t-mac81/pi-weather-station/images/IMG_1845.jpg

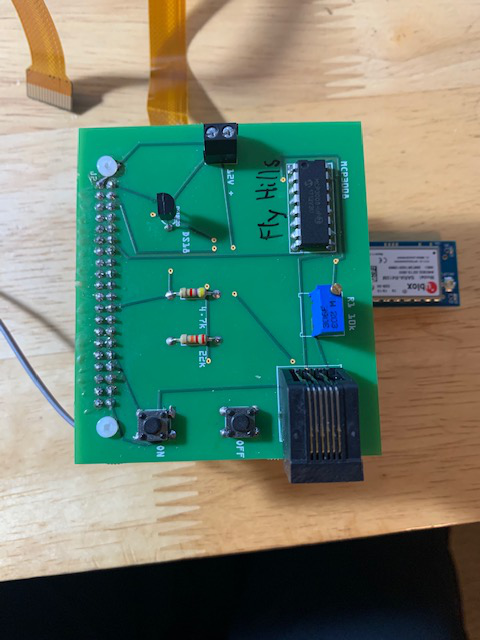
images/IMG_1845.jpg
