t-mac81/pi-weather-station/images/IMG_1846.jpg

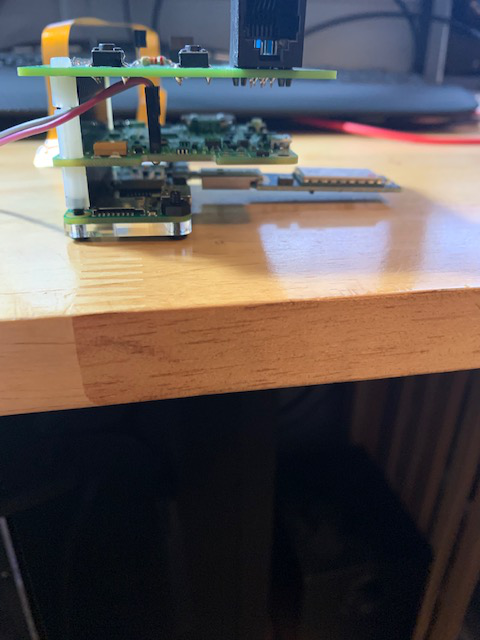
images/IMG_1846.jpg
