t-mac81/pi-weather-station/images/IMG_2492.JPG

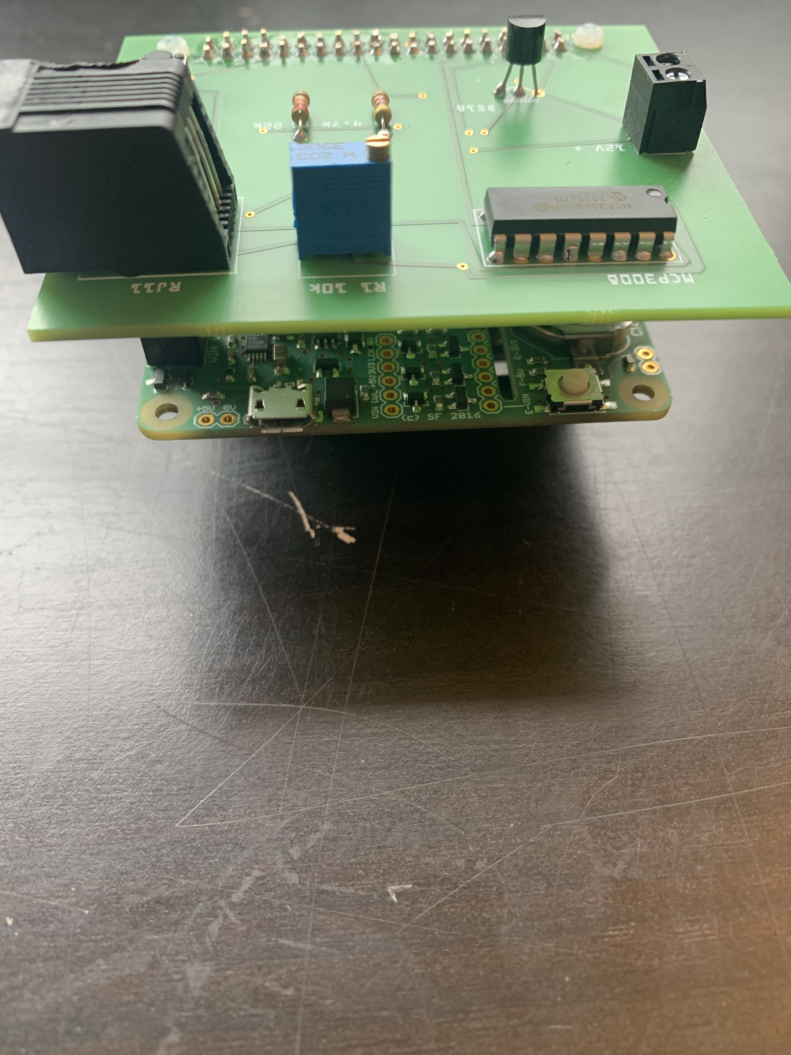
images/IMG_2492.JPG
