t-mac81/pi-weather-station/images/IMG_2493.JPG

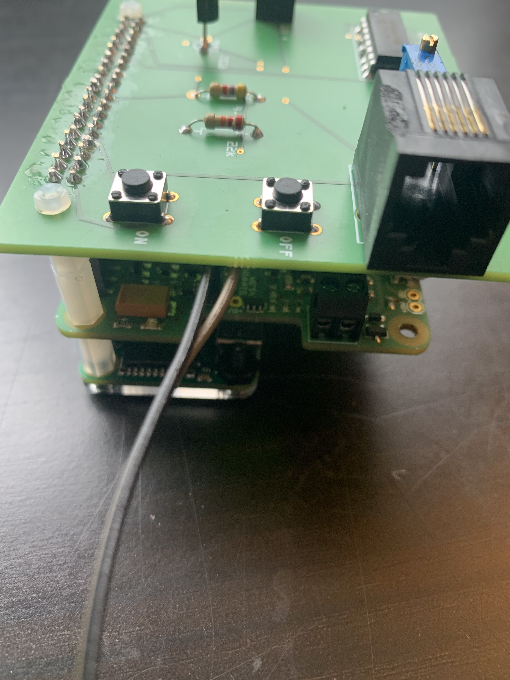
images/IMG_2493.JPG
