t-mac81/pi-weather-station/images/IMG_2494.JPG

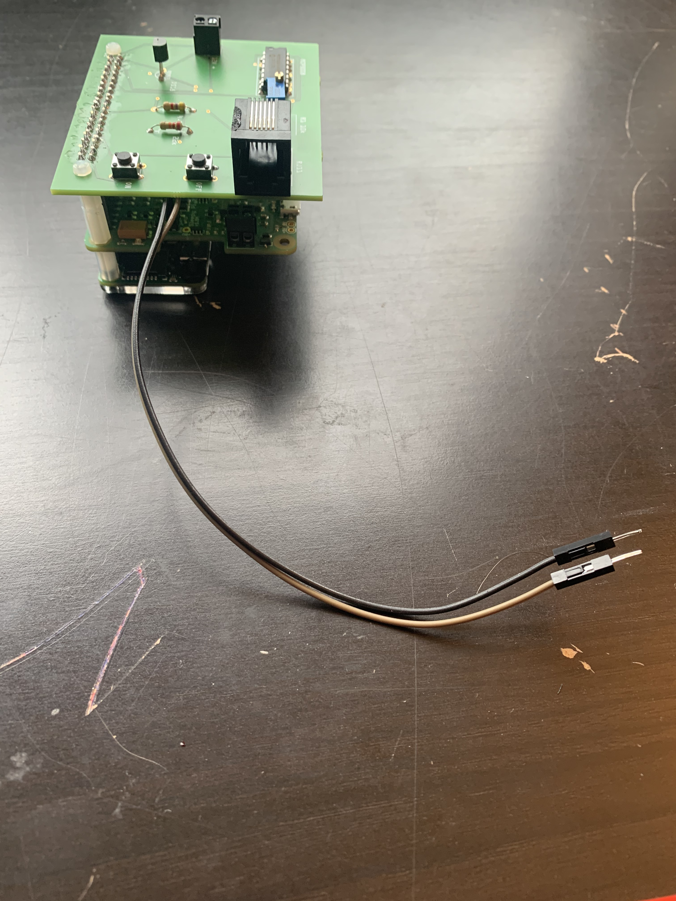
images/IMG_2494.JPG
