t-mac81/pi-weather-station/images/IMG_2495.JPG

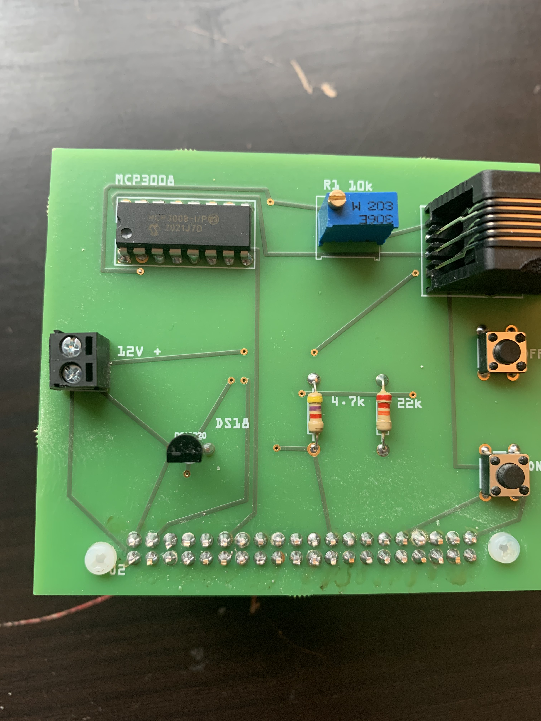
images/IMG_2495.JPG
