t-mac81/pi-weather-station/images/IMG_2496.JPG

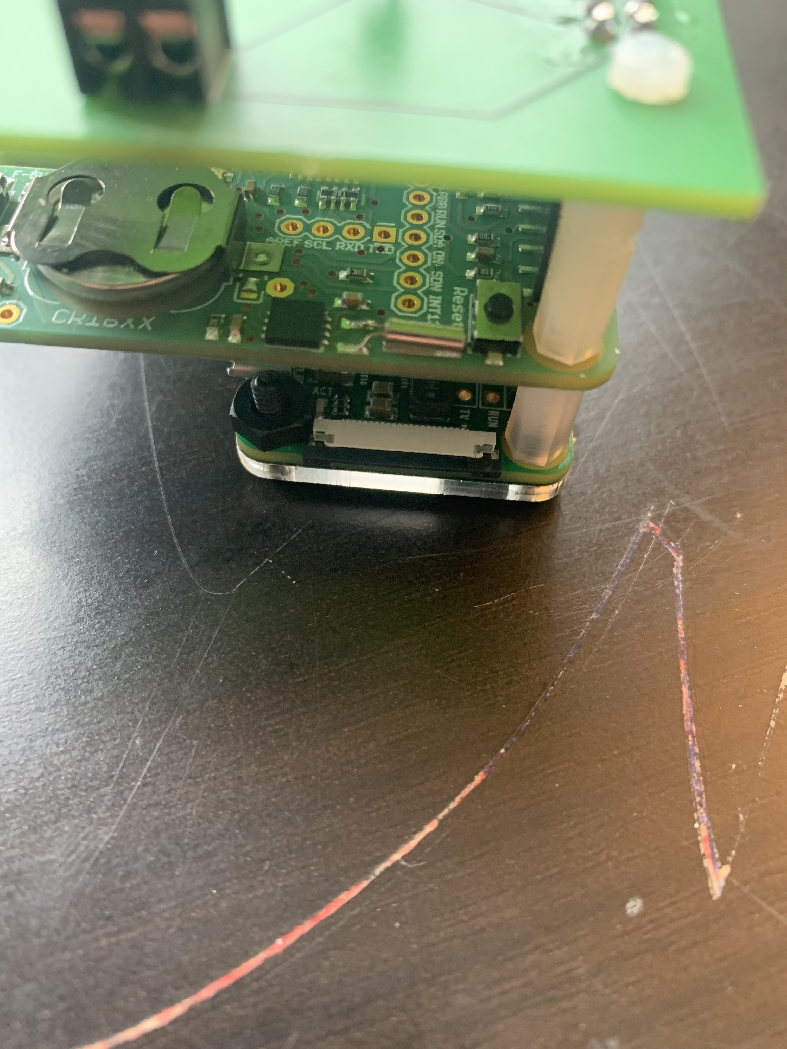
images/IMG_2496.JPG
